TychoJ/sigprocHvA/analoog/LTspice/Draft2.asc

C1: cap; 390n
C2: cap; 4.7µ
C3: cap; 100n
R1: res; 10k
R2: res; 10k
R3: res; 230
R4: res; 10k
R5: res; 4.3k
U1: UniversalOpAmp2
U2: UniversalOpAmp2
V1: voltage; ""; AC 1; Rser=50
V2: voltage; 100
V3: voltage; 100
Named nets: 0, IN, OUT
.ac dec 100 0.1 1k
